JDHinds/ELE2025/MotorDriverExercise/coasting.ino

#define M1A 3 //M1A is connected to Arduino pin 3
#define M1B 5 //M1B is connected to Arduino pin 5

void setup() {
}
void loop() {
    analogWrite(M1A, 0);
    analogWrite(M1B, 0);
    for (int i = 0; i < 256; i++)
    {
        analogWrite(M1A, i);
        delay(200);
    }
    analogWrite(M1B, 255);
    delay(5000);
}
